TeknoTrek/LC-Meter/materiel/inductor axial 10uH.STEP

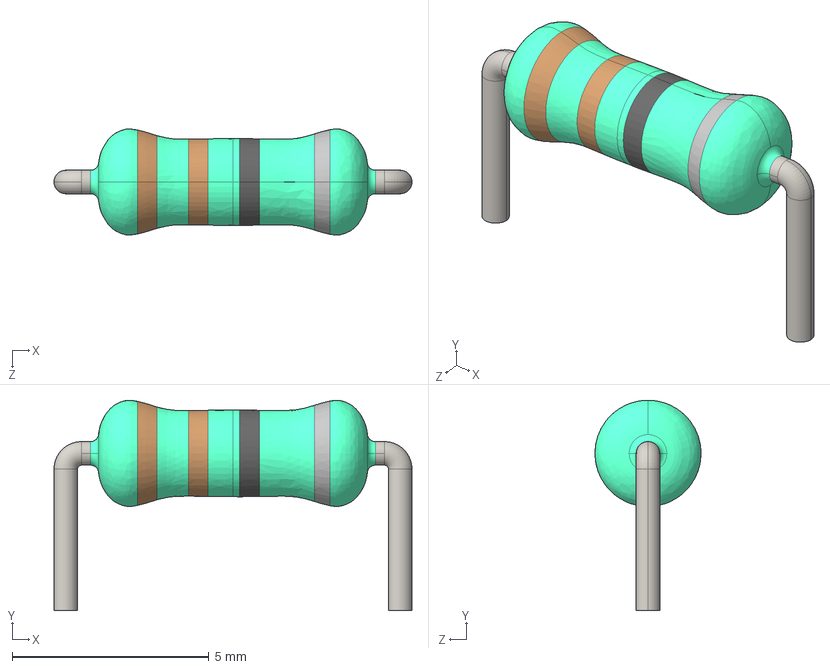
[picture p17: CAD file, 2024-11-26]
materiel/inductor axial 10uH.STEP
9.10 x 5.35 x 2.70 mm
