TeknoTrek/LC-Meter/materiel/Cap Tan TH –Leads L12mm Radial Dipped T350.stp

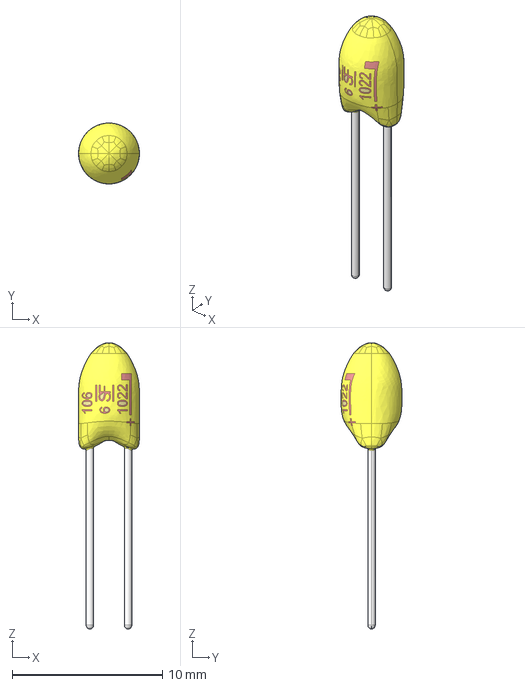
[picture p18: CAD file, 2024-11-26]
materiel/Cap Tan TH –Leads L12mm Radial Dipped T350.stp
4.06 x 4.06 x 19.0 mm
