TeknoTrek/LC-Meter/materiel/KLS7_TS1204_12x12.step

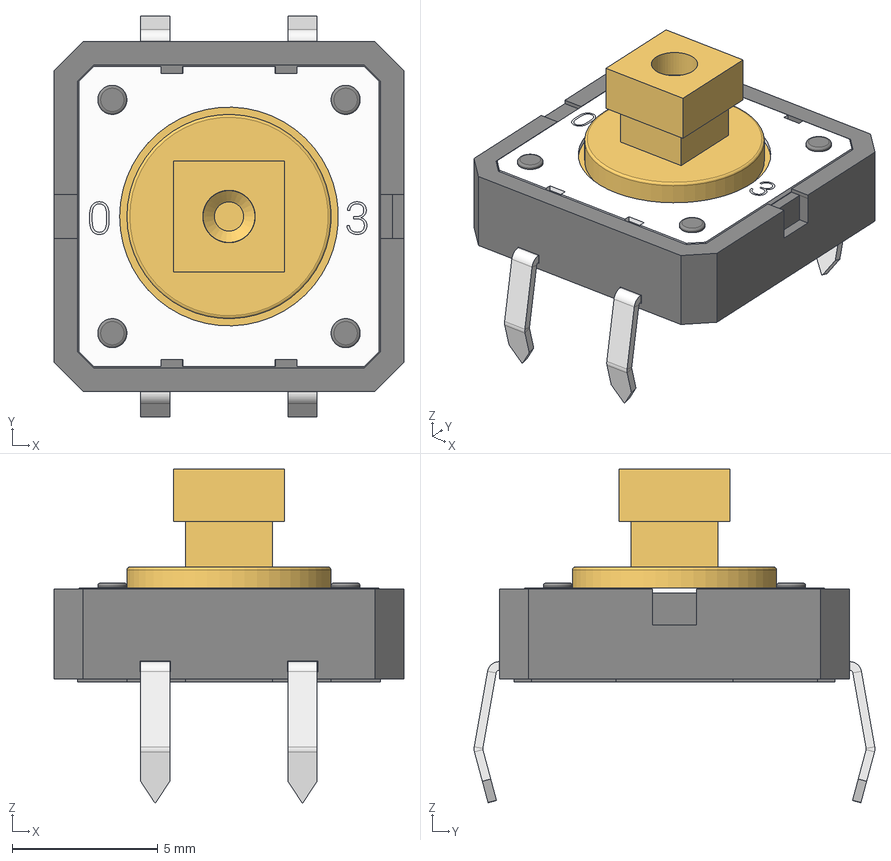
[picture p19: CAD file, 2024-11-26]
materiel/KLS7_TS1204_12x12.step
12.0 x 13.7 x 11.4 mm
Head
Pin001_002
Pin003_004
Metal_plate
dig_3
dig_0
T3F
Isolator
Contact_plate
