TeknoTrek/LC-Meter/materiel/1602 LCD.stp

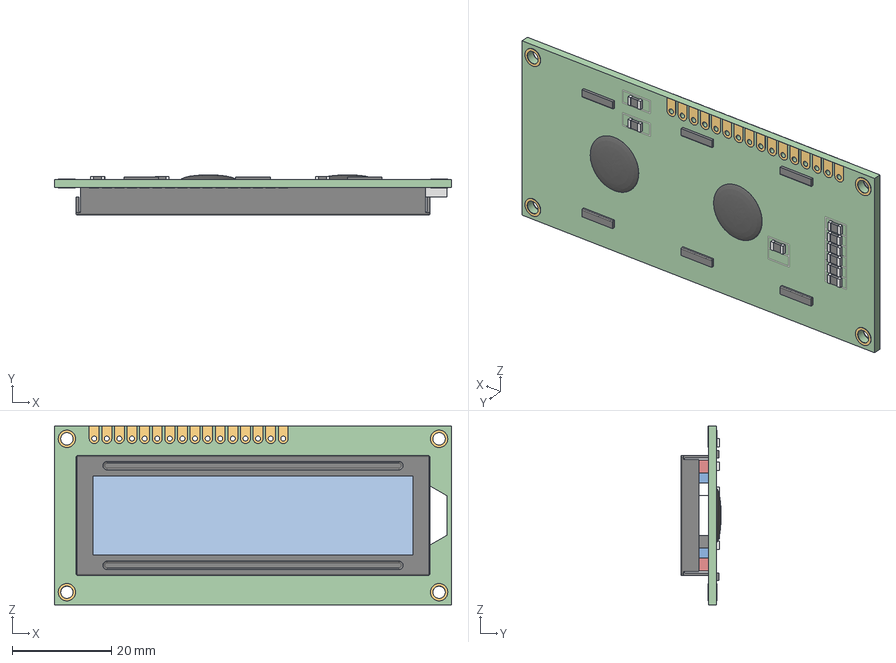
[picture p20: CAD file, 2024-11-26]
materiel/1602 LCD.stp
80.0 x 8.10 x 36.0 mm
PCB
Mounting Screw Ring x 6
Mounting Screw Ring_mir x 2
Wire Connector Plating x 32
SMD_R 1206 Body x 9
SMD_R 1206 Connector x 18
LCD Conductive Band x 2
LCD Screen
LCD Glass
Round Chip x 2
LCD Frame
