TeknoTrek/LC-Meter/materiel/OMRON B3F 12mm TACT SWITCH.STEP

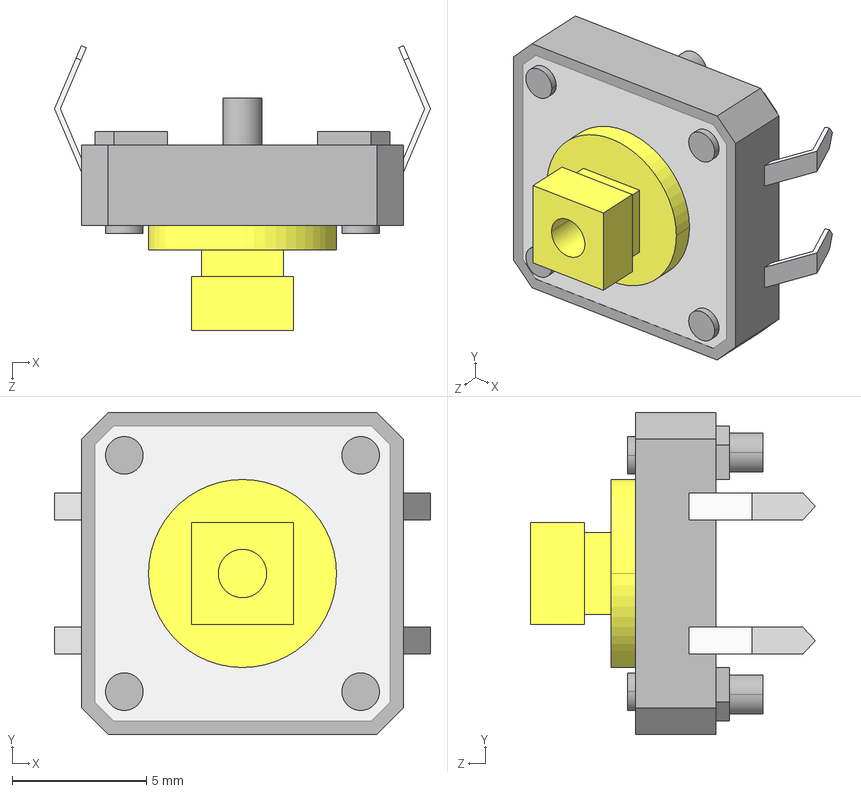
[picture p21: CAD file, 2024-11-26]
materiel/OMRON B3F 12mm TACT SWITCH.STEP
14.0 x 12.0 x 10.6 mm
